ROCO504/2018-Group2/Pictures and Videos/CompletedRobot.jpg

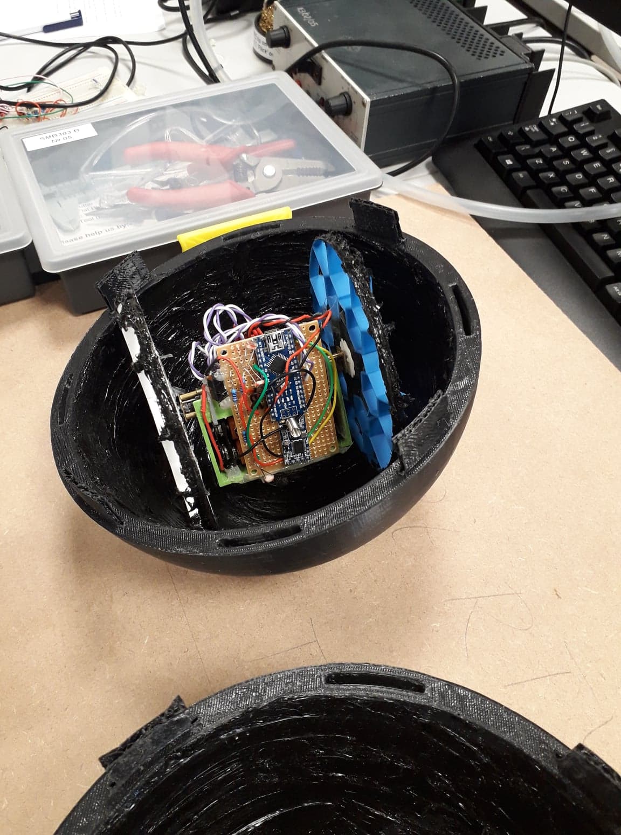
Pictures and Videos/CompletedRobot.jpg
