ROCO504/2018-Group2/Pictures and Videos/Prototype Screenshot.PNG

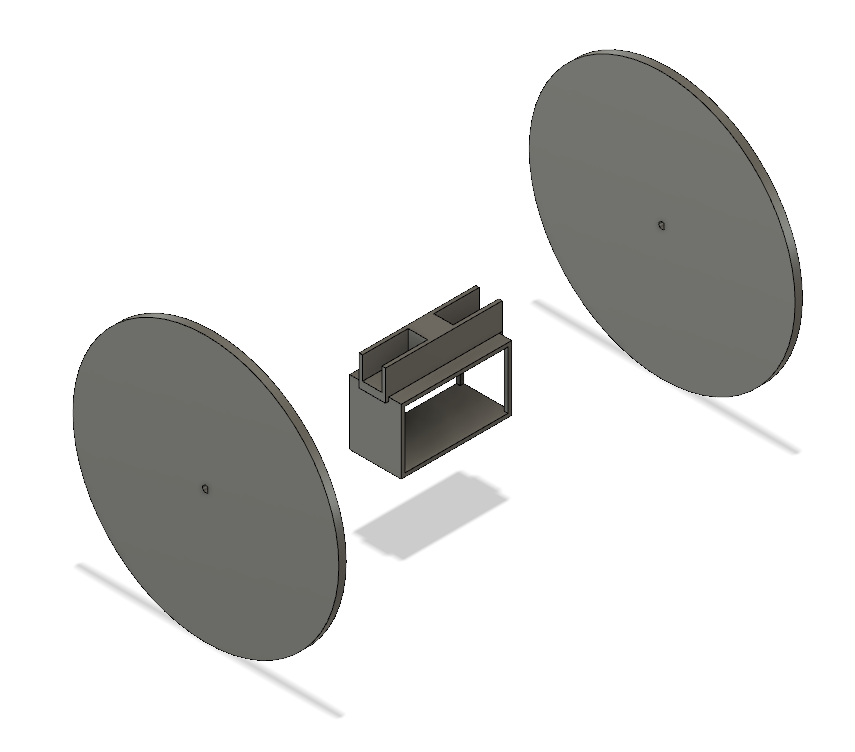
Pictures and Videos/Prototype Screenshot.PNG
