ROCO504/2018-Group2/Pictures and Videos/SketchPhotos/42857456_2206434372946525_2190744581534908416_n.jpg

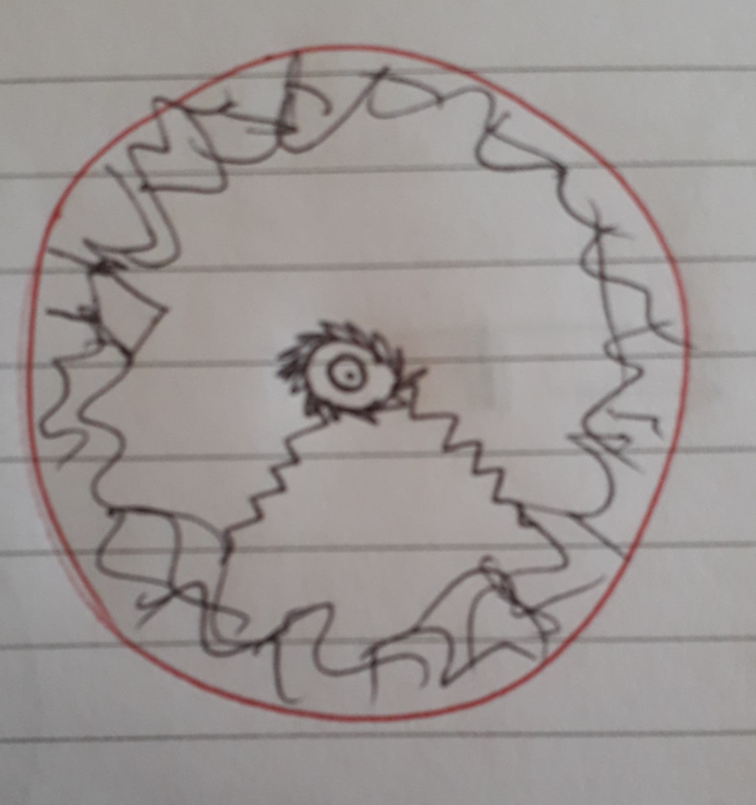
Pictures and Videos/SketchPhotos/42857456_2206434372946525_2190744581534908416_n.jpg
