ROCO504/2018-Group2/Pictures and Videos/SketchPhotos/42906171_2155153138085306_803685275543797760_n.jpg

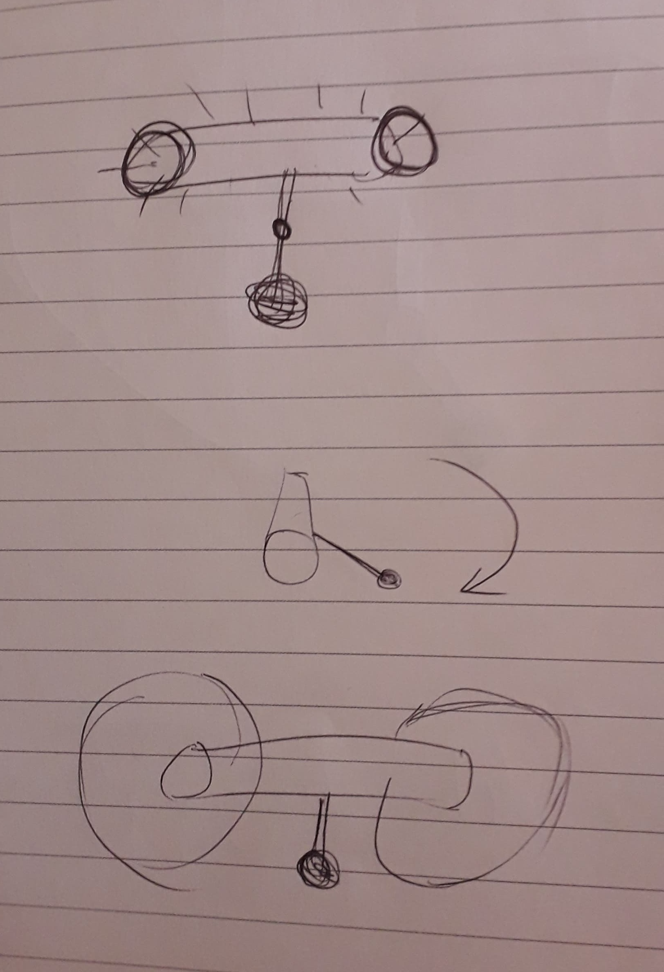
Pictures and Videos/SketchPhotos/42906171_2155153138085306_803685275543797760_n.jpg
