ROCO504/2018-Group2/Pictures and Videos/SketchPhotos/42916007_303731217091233_7673987877885181952_n.jpg

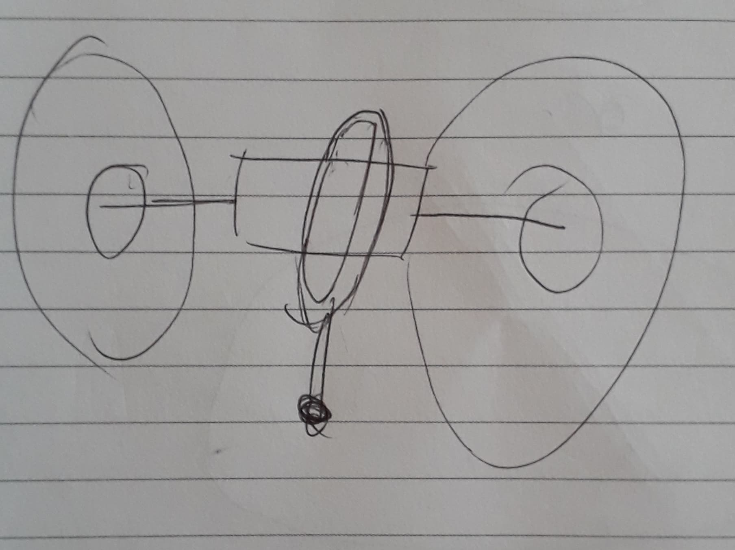
Pictures and Videos/SketchPhotos/42916007_303731217091233_7673987877885181952_n.jpg
