ROCO504/2018-Group2/Pictures and Videos/SketchPhotos/42943255_2012901992081893_4866297675508613120_n.jpg

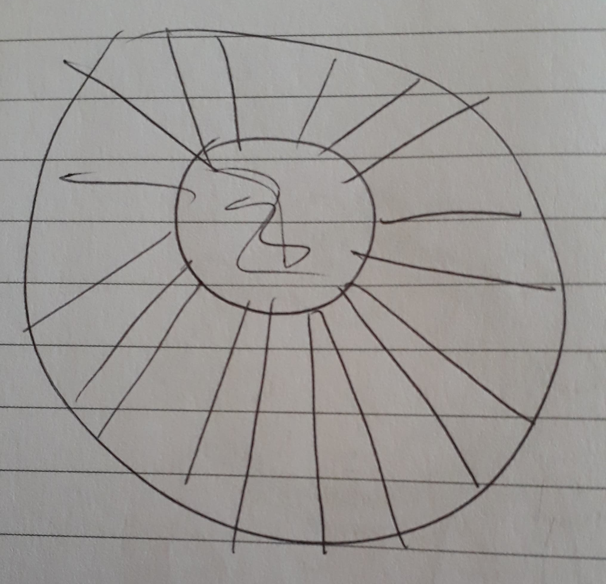
Pictures and Videos/SketchPhotos/42943255_2012901992081893_4866297675508613120_n.jpg
