ROCO504/2018-Group2/Pictures and Videos/SketchPhotos/42951792_1894298790687516_956359517396795392_n.jpg

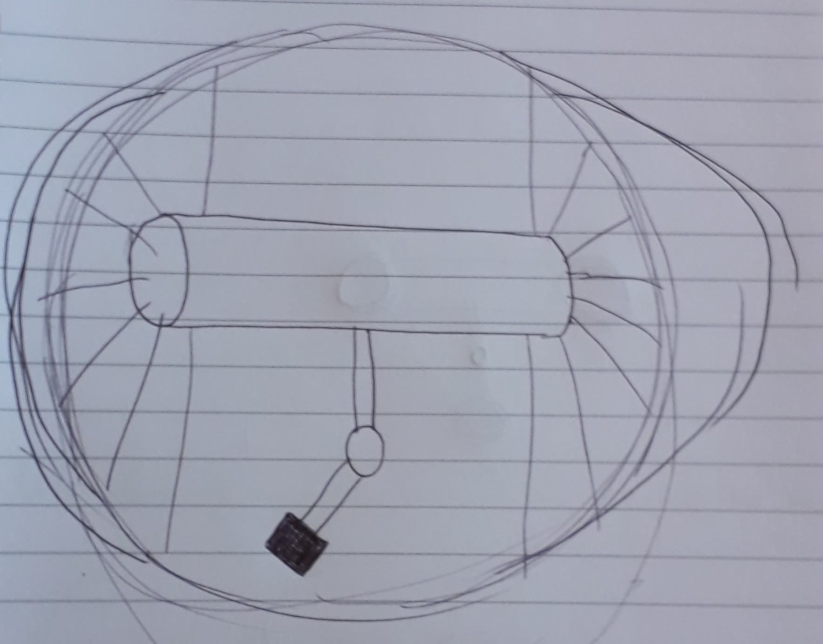
Pictures and Videos/SketchPhotos/42951792_1894298790687516_956359517396795392_n.jpg
