ROCO504/2018-Group2/Pictures and Videos/SketchPhotos/42970392_149661312643294_5381563583454773248_n.jpg

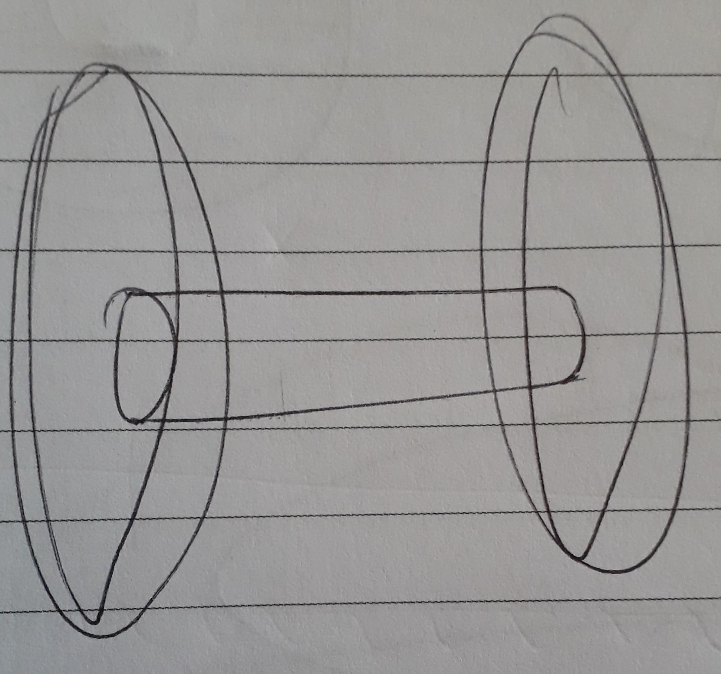
Pictures and Videos/SketchPhotos/42970392_149661312643294_5381563583454773248_n.jpg
