ROCO504/2018-Group2/Pictures and Videos/SketchPhotos/42982693_491175638065149_2728994654778294272_n.jpg

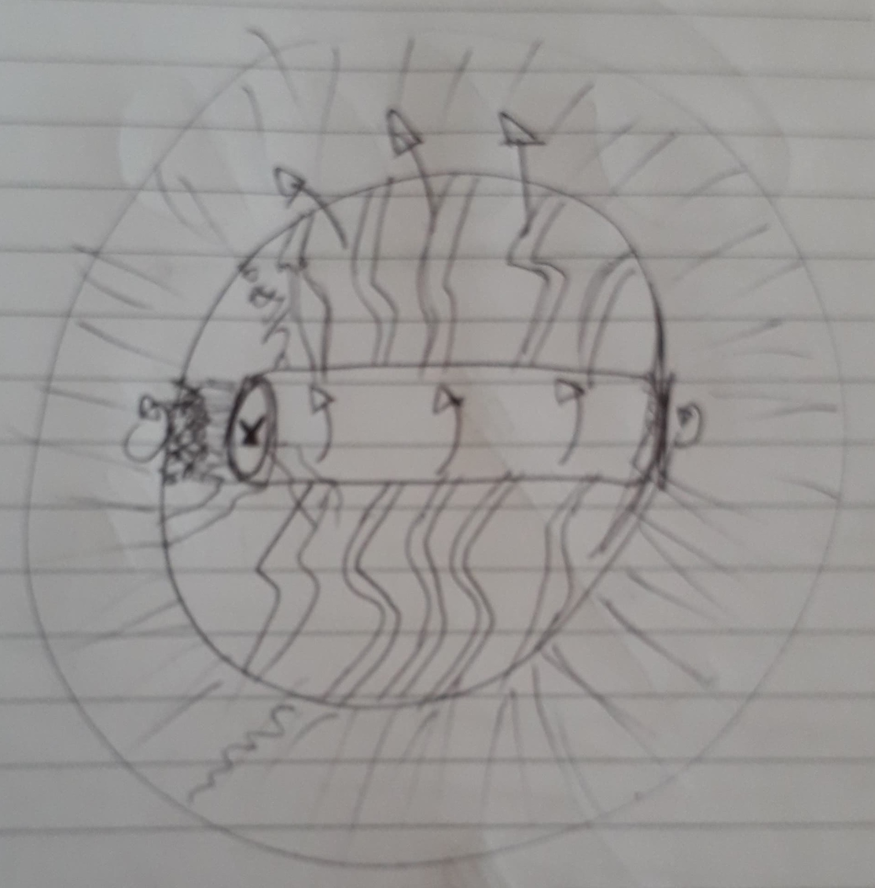
Pictures and Videos/SketchPhotos/42982693_491175638065149_2728994654778294272_n.jpg
