ROCO504/2018-Group2/Pictures and Videos/SketchPhotos/43074571_290849058420375_7525813348714151936_n.jpg

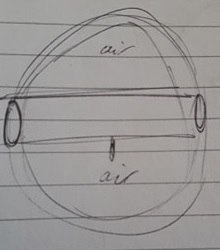
Pictures and Videos/SketchPhotos/43074571_290849058420375_7525813348714151936_n.jpg
