ROCO504/2018-Group2/Simulations/FEA and Material Resources/NinjaFlexProperties.PNG

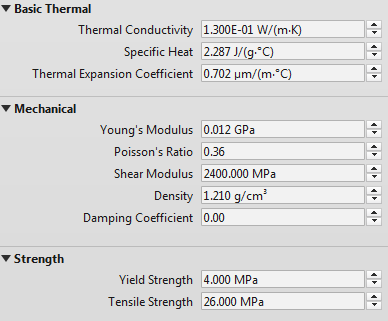
Simulations/FEA and Material Resources/NinjaFlexProperties.PNG
