ROCO504/2018-Group2/Simulations/FEA and Material Resources/SandFlea1mmSim/50N v1.png

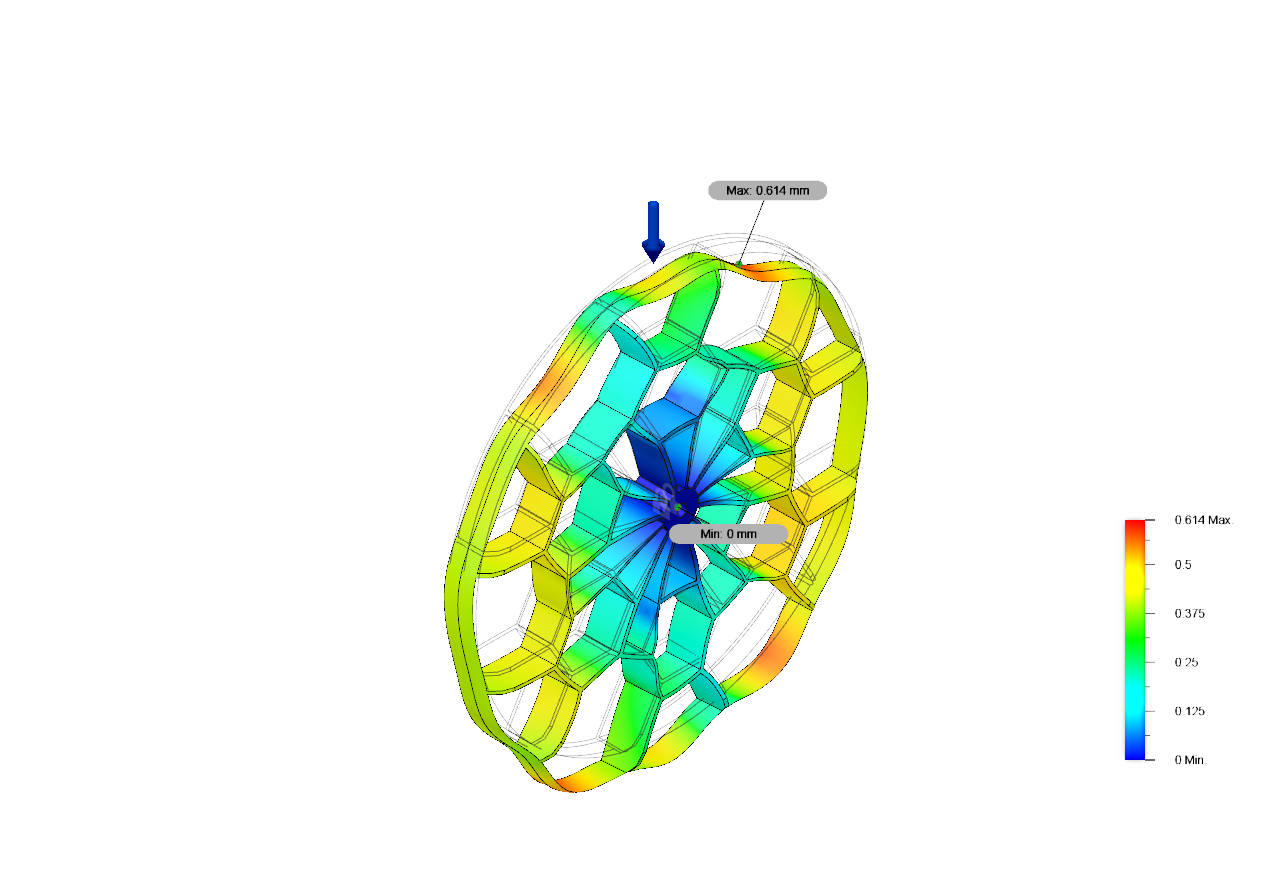
Simulations/FEA and Material Resources/SandFlea1mmSim/50N v1.png
