ROCO504/2018-Group2/Simulations/FEA and Material Resources/SphereSim/NinjaFlex.png

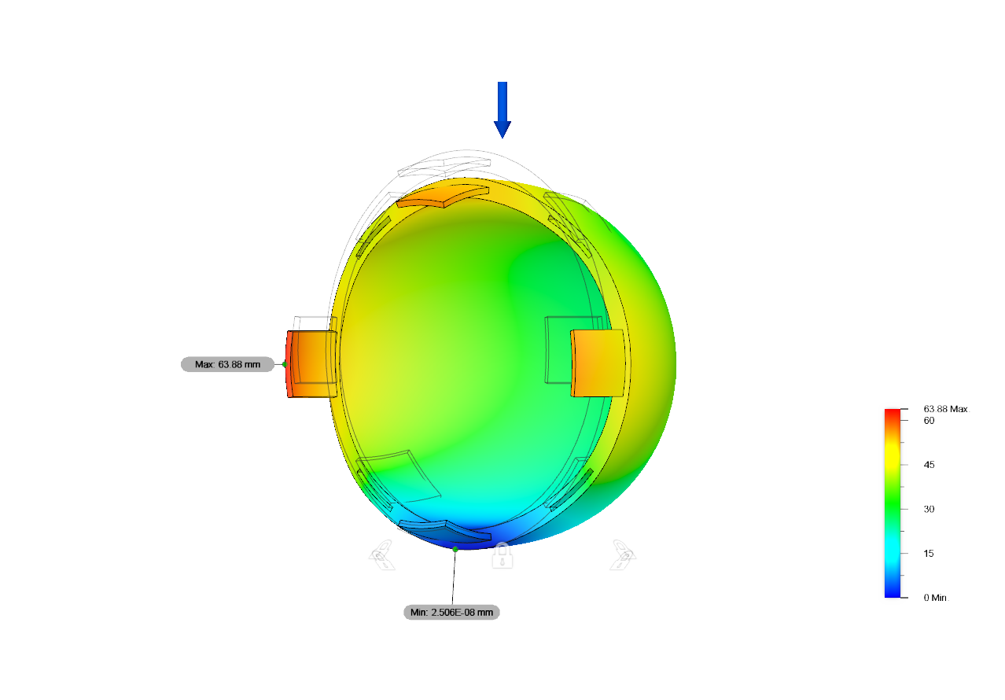
Simulations/FEA and Material Resources/SphereSim/NinjaFlex.png
