ROCO504/2018-Group2/Simulations/FEA and Material Resources/TyreSim/50N v2.png

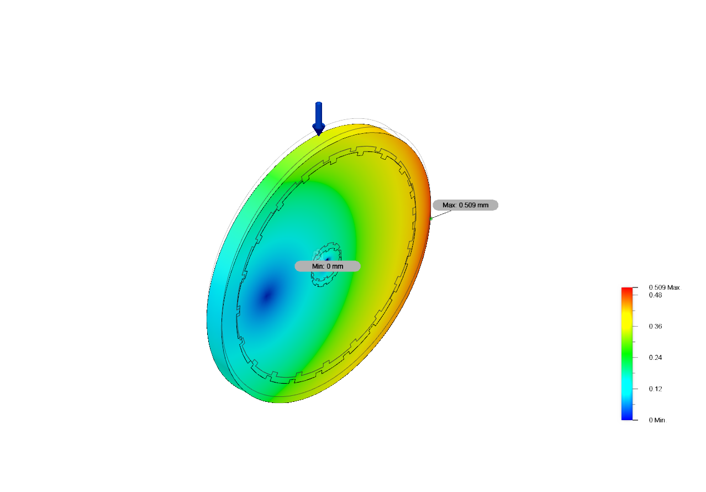
Simulations/FEA and Material Resources/TyreSim/50N v2.png
