ROCO504/2018-Group2/Simulations/FEA and Material Resources/TyreSim/100N.png

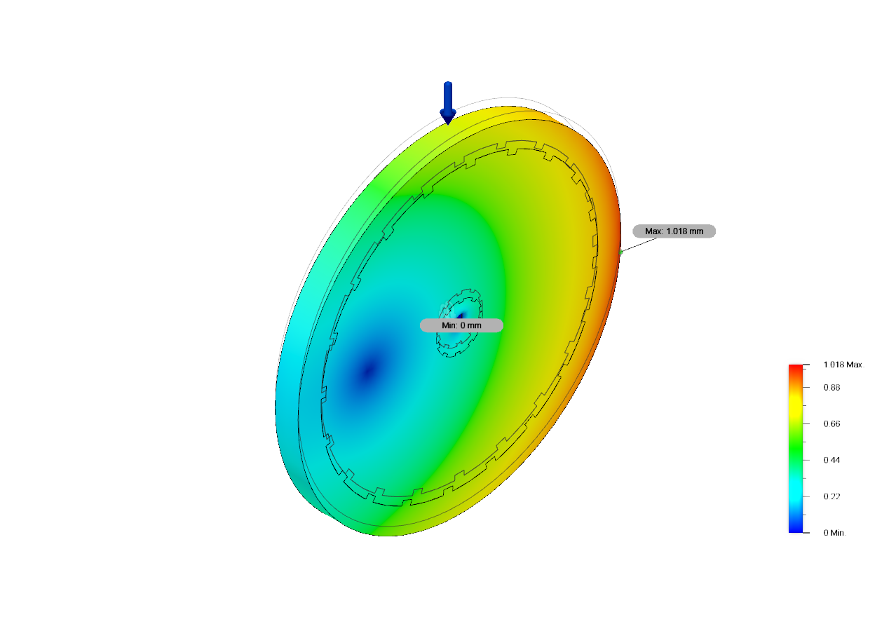
Simulations/FEA and Material Resources/TyreSim/100N.png
