ROCO504/2018-Group2/3D Prints/Test Flex v2.step

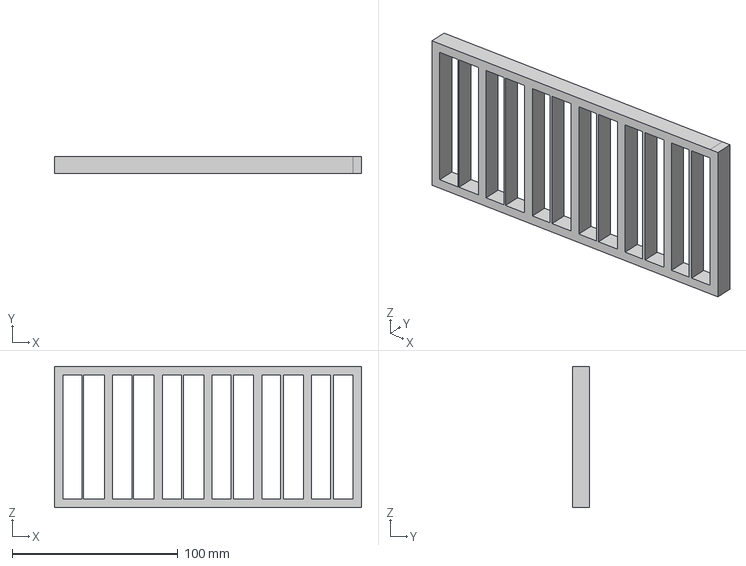
[picture p50: CAD file, 2019-01-08]
3D Prints/Test Flex v2.step
185.0 x 10.0 x 85.0 mm
