ROCO504/2018-Group2/3D Prints/FlexiSphereTest.step

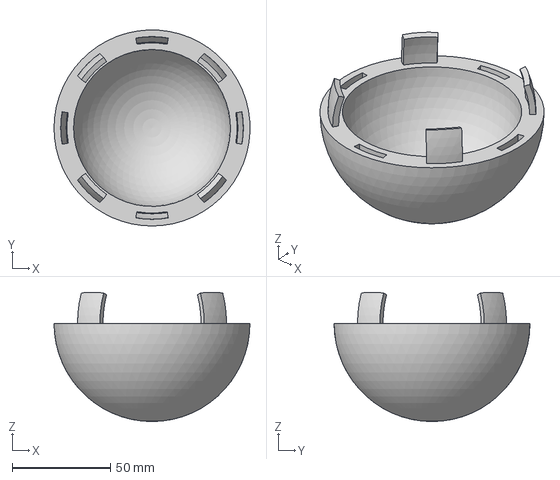
[picture p51: CAD file, 2019-01-08]
3D Prints/FlexiSphereTest.step
100.0 x 100.0 x 65.9 mm
