ROCO504/2018-Group2/3D Prints/SmallSolidFlex.step

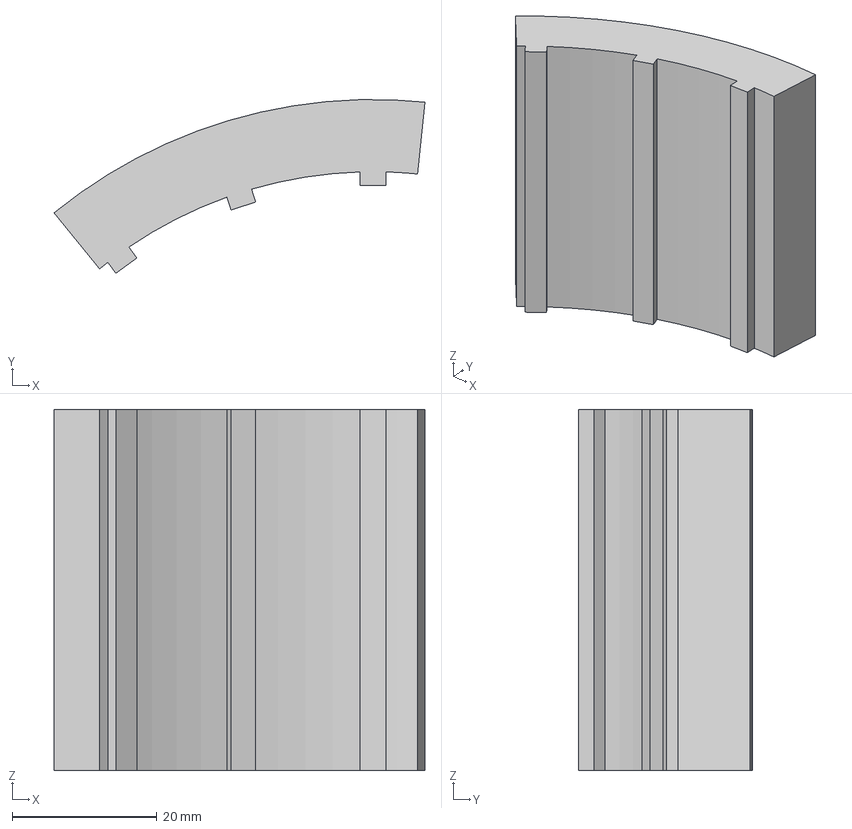
[picture p52: CAD file, 2019-01-08]
3D Prints/SmallSolidFlex.step
51.3 x 24.0 x 50.0 mm
