ROCO504/2018-Group2/3D Prints/FlexInner.step

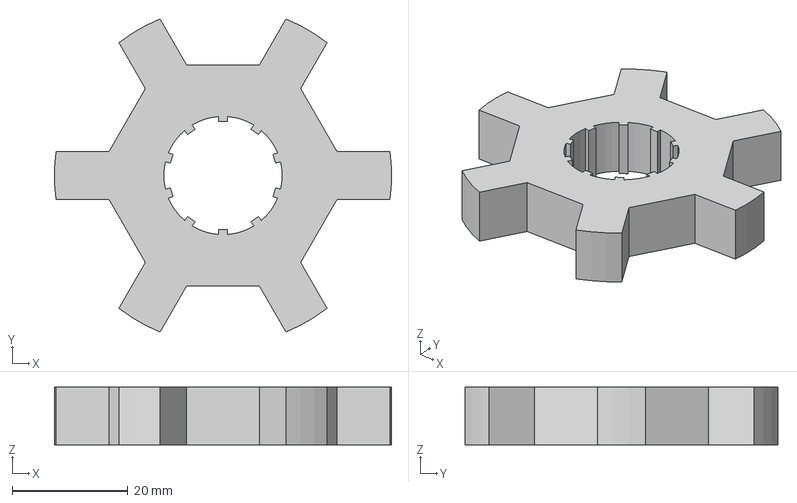
[picture p53: CAD file, 2019-01-08]
3D Prints/FlexInner.step
58.1 x 54.0 x 10.0 mm
