ROCO504/2018-Group2/3D Prints/OUTERFLEX thin v1.step

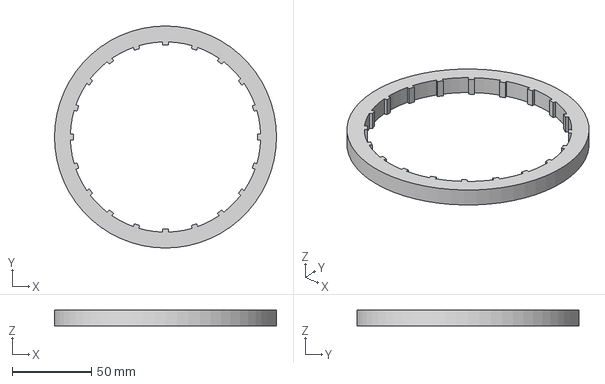
[picture p54: CAD file, 2019-01-08]
3D Prints/OUTERFLEX thin v1.step
140.0 x 140.0 x 10.0 mm
