ROCO504/2018-Group2/3D Prints/OuterPLA.step

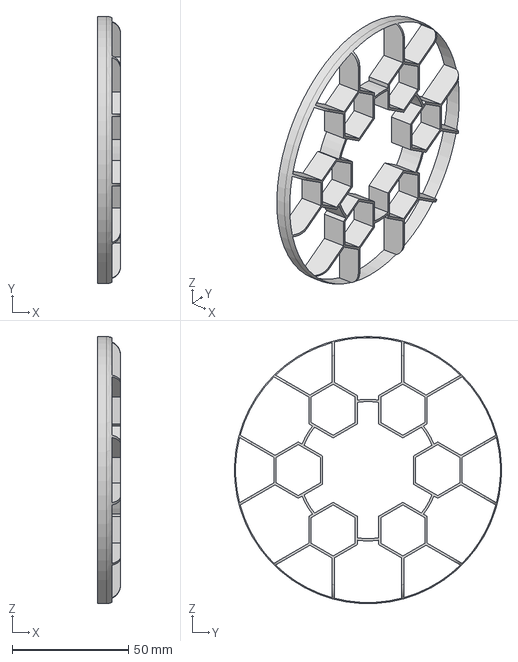
[picture p55: CAD file, 2019-01-08]
3D Prints/OuterPLA.step
10.0 x 115.0 x 114.9 mm
